pmgducati/Blue-Retro-Single-Console-Units/PCB/CD-i.brd

## EAGLE design PCB/CD-i.brd (2022-05-03)

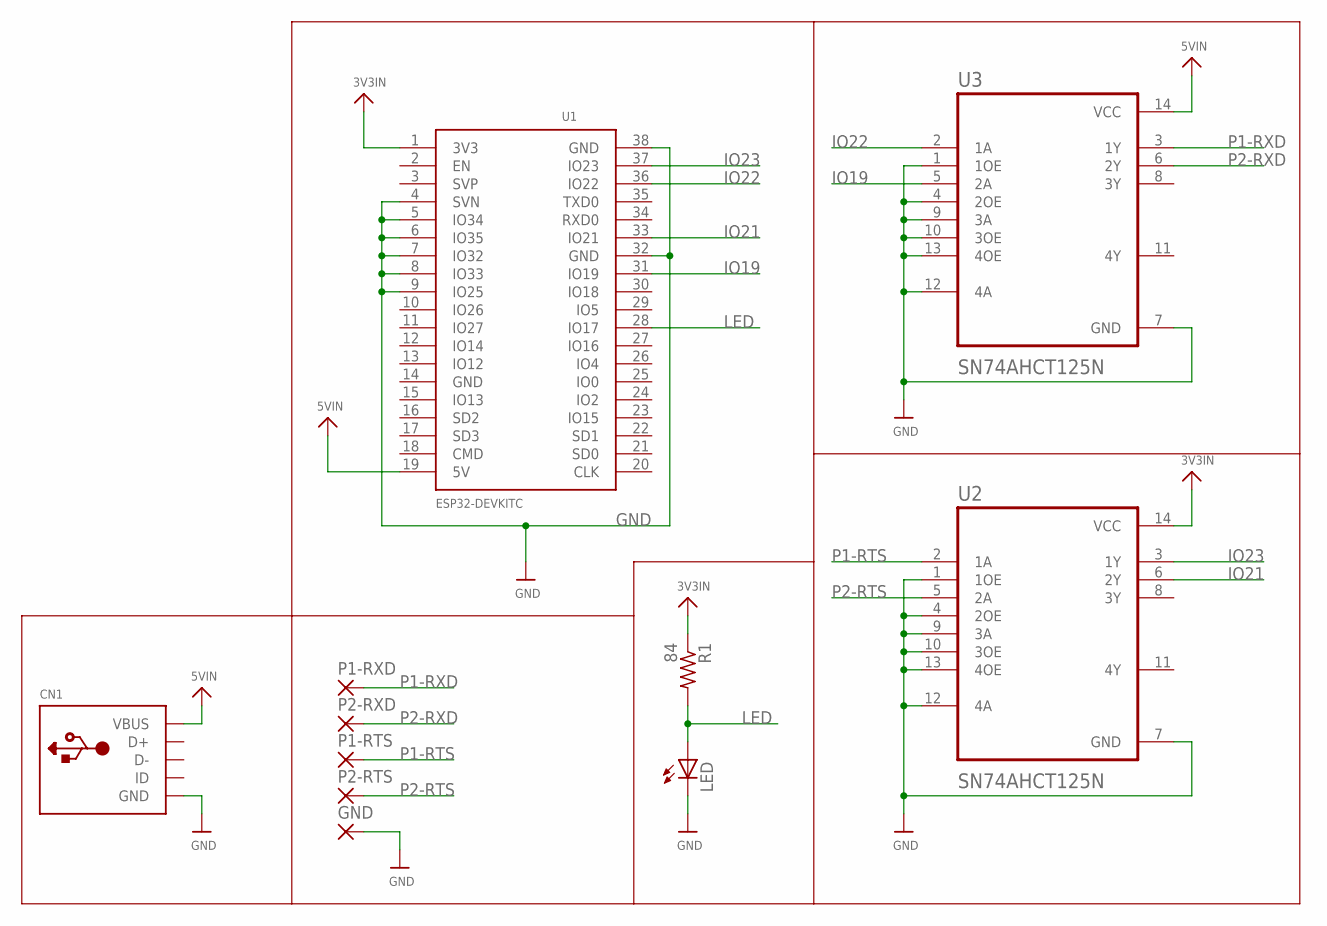
[picture p23: schematic CD-i.sch]

Parts:
CN1: USBTHM; USB-MINIB-THM
GND: SMD5; SMD2,54-5,08
LED: LEDCHIPLED_1206; CHIPLED_1206
P1-RTS, P1-RXD, P2-RTS, P2-RXD: SMD5; SMD2,54-5,08
R1: 84; R1206
U1: ESP32DEVKITC; ESP32-DEVKITC
U2, U3: SN74AHCT125N; DIP794W45P254L1969H508Q14

Connections:
3V3IN: R1.1, U1.1 (3V3), U2.14 (VCC)
5VIN: CN1.VBUS, U1.19 (5V), U3.14 (VCC)
GND: CN1.GND, GND.1, LED.C, U1.4 (SVN), U1.5 (IO34), U1.6 (IO35), U1.7 (IO32), U1.8 (IO33), U1.9 (IO25), U1.32 (GND), U1.38 (GND), U2.1 (1OE), U2.4 (2OE), U2.7 (GND), U2.9 (3A), U2.10 (3OE), U2.12 (4A), U2.13 (4OE), U3.1 (1OE), U3.4 (2OE), U3.7 (GND), U3.9 (3A), U3.10 (3OE), U3.12 (4A), U3.13 (4OE)
IO19: U1.31 (IO19), U3.5 (2A)
IO21: U1.33 (IO21), U2.6 (2Y)
IO22: U1.36 (IO22), U3.2 (1A)
IO23: U1.37 (IO23), U2.3 (1Y)
LED: LED.A, R1.2, U1.28 (IO17)
P1-RTS: P1-RTS.1, U2.2 (1A)
P1-RXD: P1-RXD.1, U3.3 (1Y)
P2-RTS: P2-RTS.1, U2.5 (2A)
P2-RXD: P2-RXD.1, U3.6 (2Y)

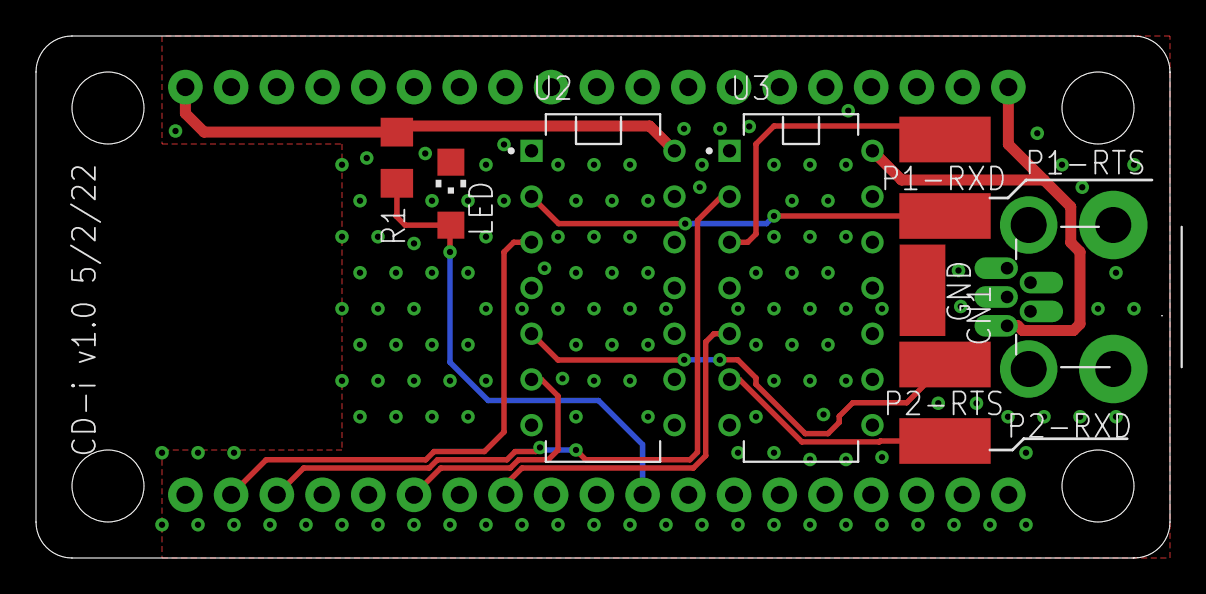
[picture p24: board CD-i.brd from above]

Board: 2 copper layers, 63.0 x 29.0 mm, 11 parts (1 on the bottom side), 12 nets.
