pmgducati/Blue-Retro-Single-Console-Units/PCB/NES.brd

## EAGLE design PCB/NES.brd (2022-05-03)

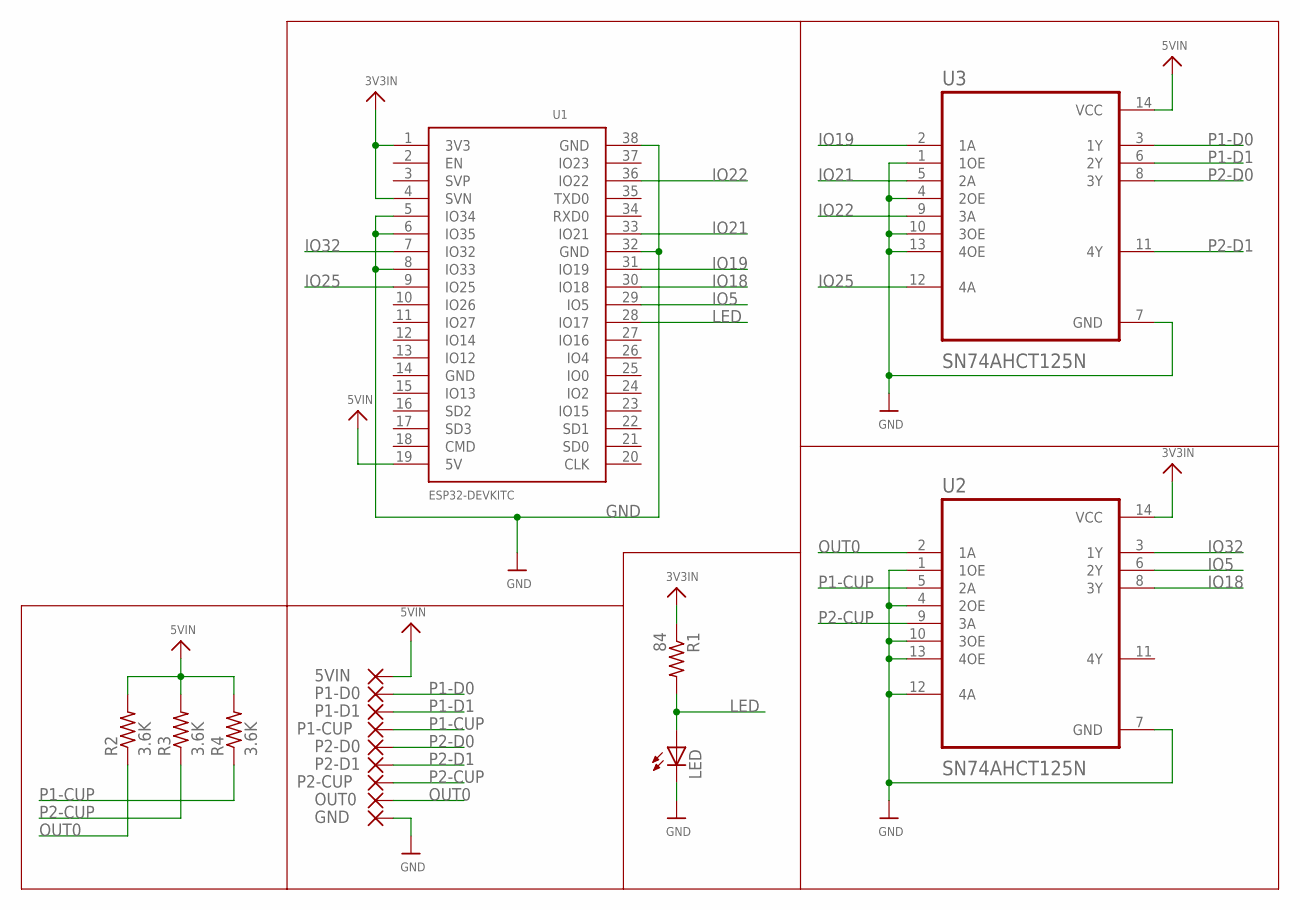
[picture p25: schematic NES.sch]

Parts:
5VIN: SMD5; SMD2,54-5,08
GND: SMD5; SMD2,54-5,08
LED: LEDCHIPLED_1206; CHIPLED_1206
OUT0: SMD5; SMD2,54-5,08
P1-CUP, P1-D0, P1-D1, P2-CUP, P2-D0, P2-D1: SMD5; SMD2,54-5,08
R1: 84; R1206
R2, R3, R4: 3.6K; R1206
U1: ESP32DEVKITC; ESP32-DEVKITC
U2, U3: SN74AHCT125N; DIP794W45P254L1969H508Q14

Connections:
3V3IN: R1.1, U1.1 (3V3), U1.4 (SVN), U2.14 (VCC)
5VIN: 5VIN.1, R2.2, R3.2, R4.2, U1.19 (5V), U3.14 (VCC)
GND: GND.1, LED.C, U1.5 (IO34), U1.6 (IO35), U1.8 (IO33), U1.32 (GND), U1.38 (GND), U2.1 (1OE), U2.4 (2OE), U2.7 (GND), U2.10 (3OE), U2.12 (4A), U2.13 (4OE), U3.1 (1OE), U3.4 (2OE), U3.7 (GND), U3.10 (3OE), U3.13 (4OE)
IO5: U1.29 (IO5), U2.6 (2Y)
IO18: U1.30 (IO18), U2.8 (3Y)
IO19: U1.31 (IO19), U3.2 (1A)
IO21: U1.33 (IO21), U3.5 (2A)
IO22: U1.36 (IO22), U3.9 (3A)
IO25: U1.9 (IO25), U3.12 (4A)
IO32: U1.7 (IO32), U2.3 (1Y)
LED: LED.A, R1.2, U1.28 (IO17)
OUT0: OUT0.1, R2.1, U2.2 (1A)
P1-CUP: P1-CUP.1, R4.1, U2.5 (2A)
P1-D0: P1-D0.1, U3.3 (1Y)
P1-D1: P1-D1.1, U3.6 (2Y)
P2-CUP: P2-CUP.1, R3.1, U2.9 (3A)
P2-D0: P2-D0.1, U3.8 (3Y)
P2-D1: P2-D1.1, U3.11 (4Y)

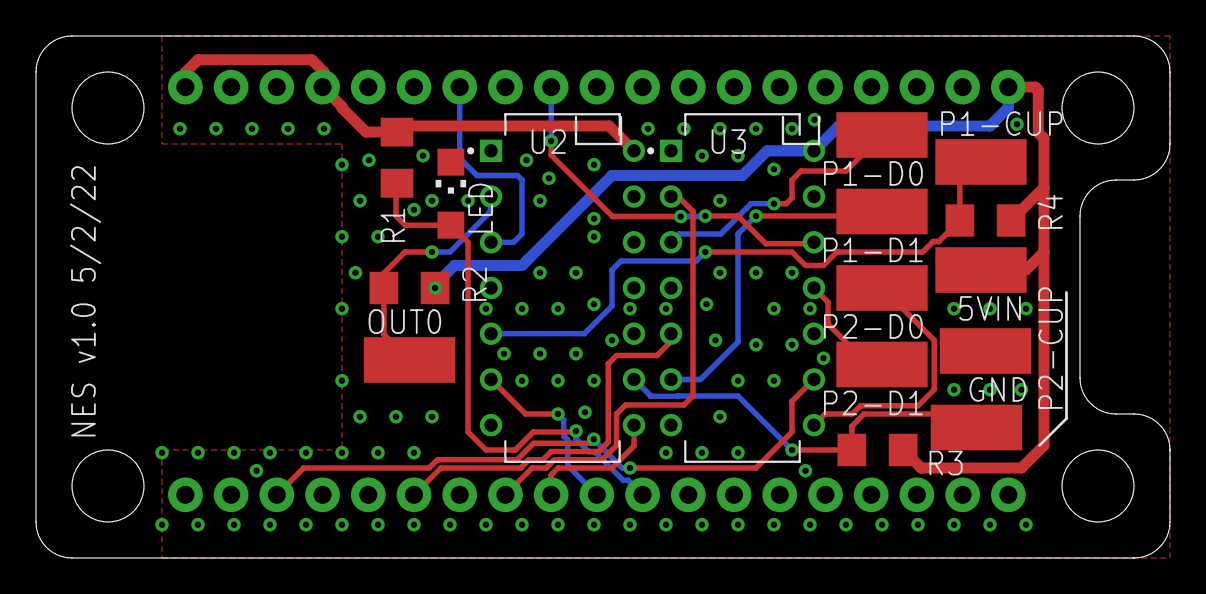
[picture p26: board NES.brd from above]

Board: 2 copper layers, 63.0 x 29.0 mm, 17 parts (1 on the bottom side), 18 nets.
