pmgducati/Blue-Retro-Single-Console-Units/PCB/3DO.brd

## EAGLE design PCB/3DO.brd (2021-10-13)

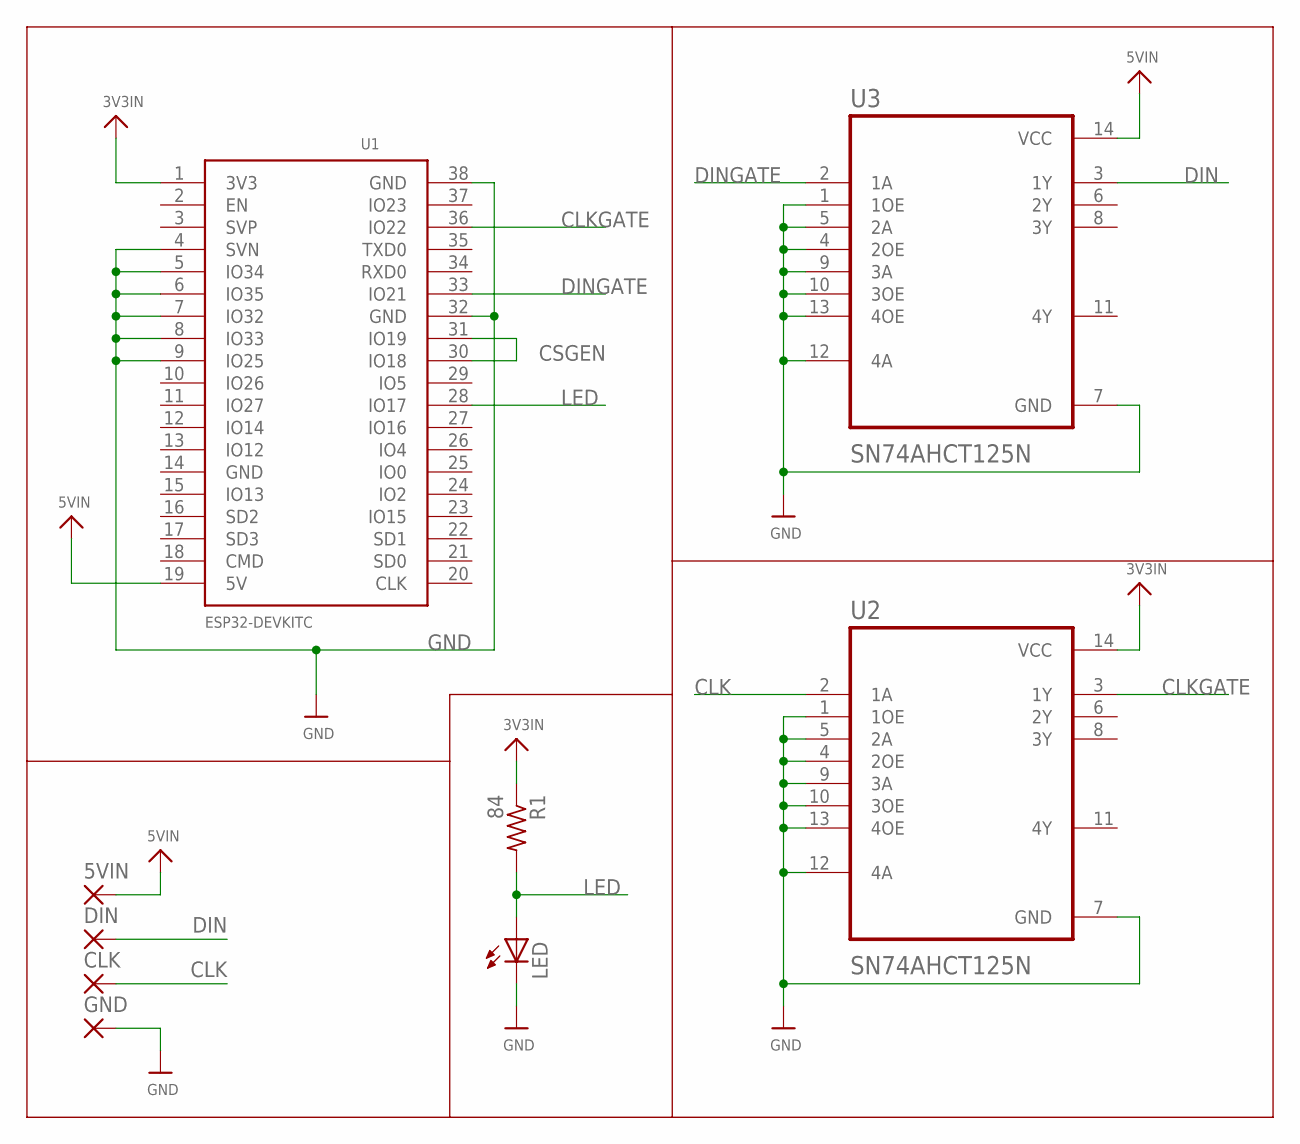
[picture p27: schematic 3DO.sch]

Parts:
5VIN: SMD5; SMD2,54-5,08
CLK: SMD5; SMD2,54-5,08
DIN: SMD5; SMD2,54-5,08
GND: SMD5; SMD2,54-5,08
LED: LEDCHIPLED_1206; CHIPLED_1206
R1: 84; R1206
U1: ESP32DEVKITC; ESP32-DEVKITC
U2, U3: SN74AHCT125N; DIP794W45P254L1969H508Q14

Connections:
3V3IN: R1.1, U1.1 (3V3), U2.14 (VCC)
5VIN: 5VIN.1, U1.19 (5V), U3.14 (VCC)
CLK: CLK.1, U2.2 (1A)
CLKGATE: U1.36 (IO22), U2.3 (1Y)
CSGEN: U1.30 (IO18), U1.31 (IO19)
DIN: DIN.1, U3.3 (1Y)
DINGATE: U1.33 (IO21), U3.2 (1A)
GND: GND.1, LED.C, U1.4 (SVN), U1.5 (IO34), U1.6 (IO35), U1.7 (IO32), U1.8 (IO33), U1.9 (IO25), U1.32 (GND), U1.38 (GND), U2.1 (1OE), U2.4 (2OE), U2.5 (2A), U2.7 (GND), U2.9 (3A), U2.10 (3OE), U2.12 (4A), U2.13 (4OE), U3.1 (1OE), U3.4 (2OE), U3.5 (2A), U3.7 (GND), U3.9 (3A), U3.10 (3OE), U3.12 (4A), U3.13 (4OE)
LED: LED.A, R1.2, U1.28 (IO17)

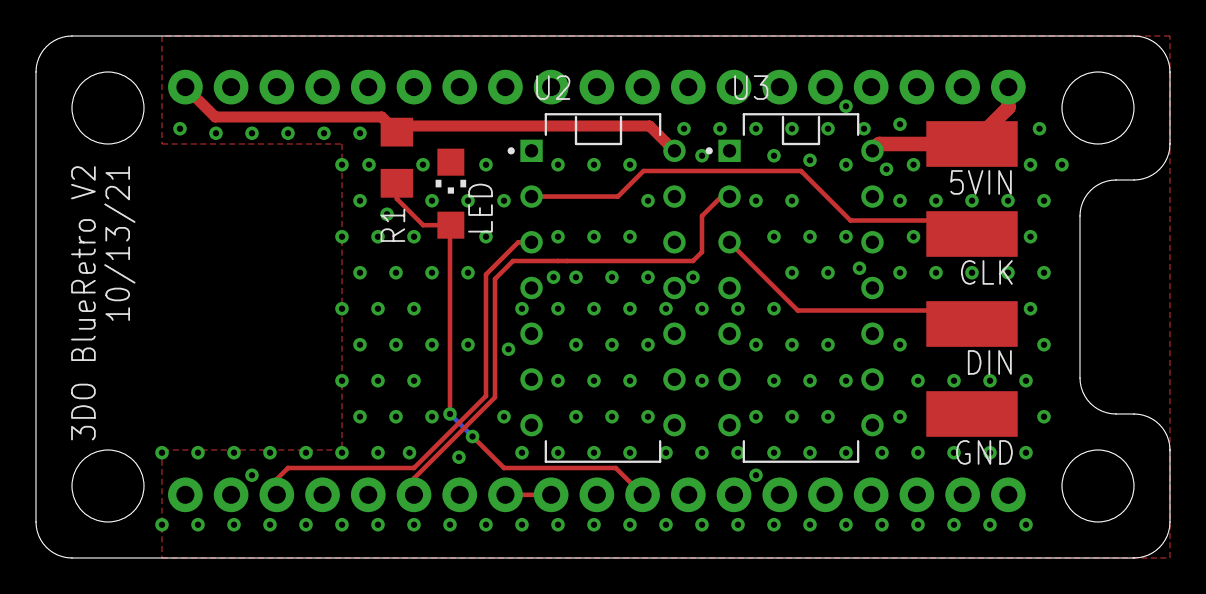
[picture p28: board 3DO.brd from above]

Board: 2 copper layers, 63.0 x 29.0 mm, 9 parts (1 on the bottom side), 9 nets.
